marcinbauer-ohf/voice-pe-casita-face/images/IMG_7611.jpeg

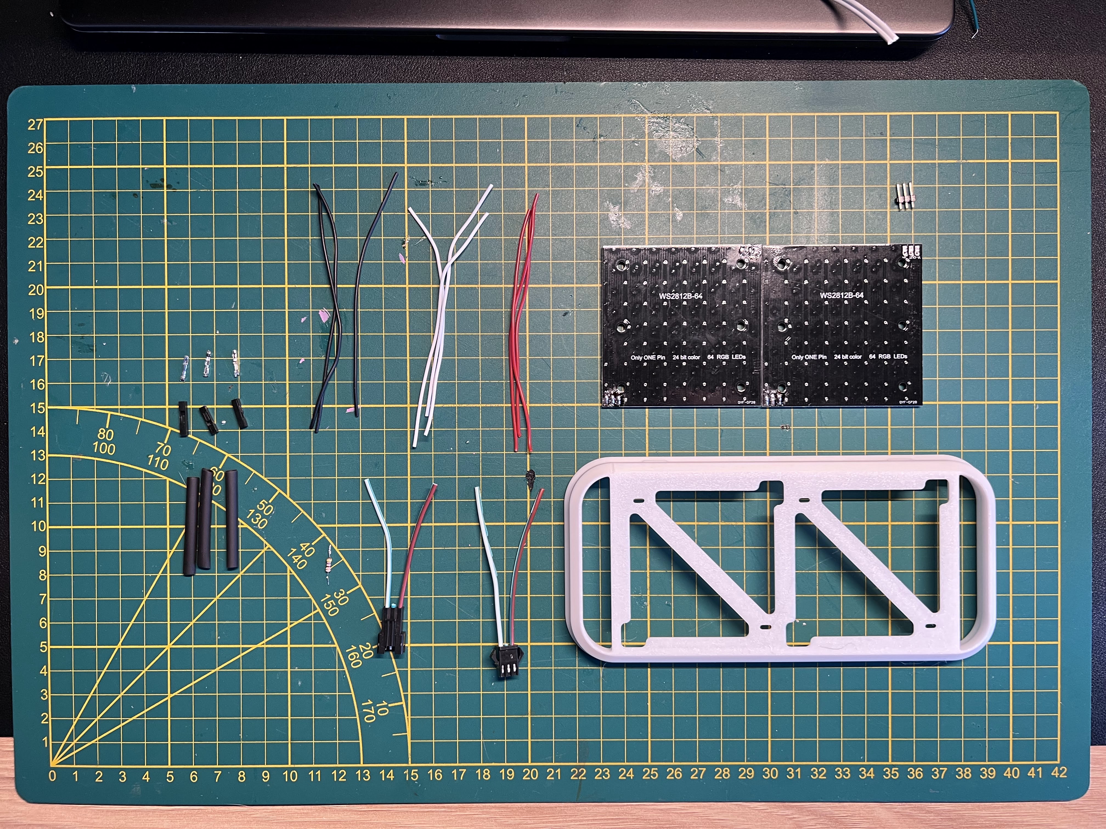
images/IMG_7611.jpeg
