marcinbauer-ohf/voice-pe-casita-face/images/IMG_7614.jpeg

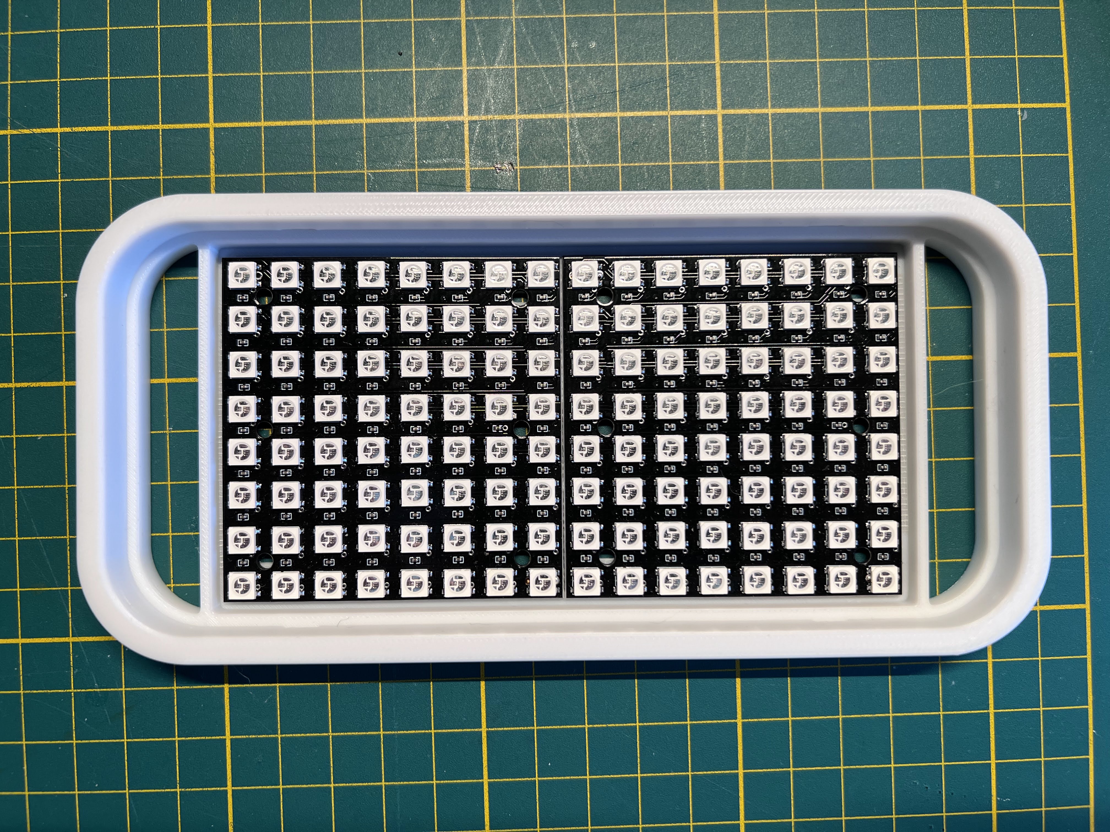
images/IMG_7614.jpeg
