marcinbauer-ohf/voice-pe-casita-face/images/IMG_7622.jpeg

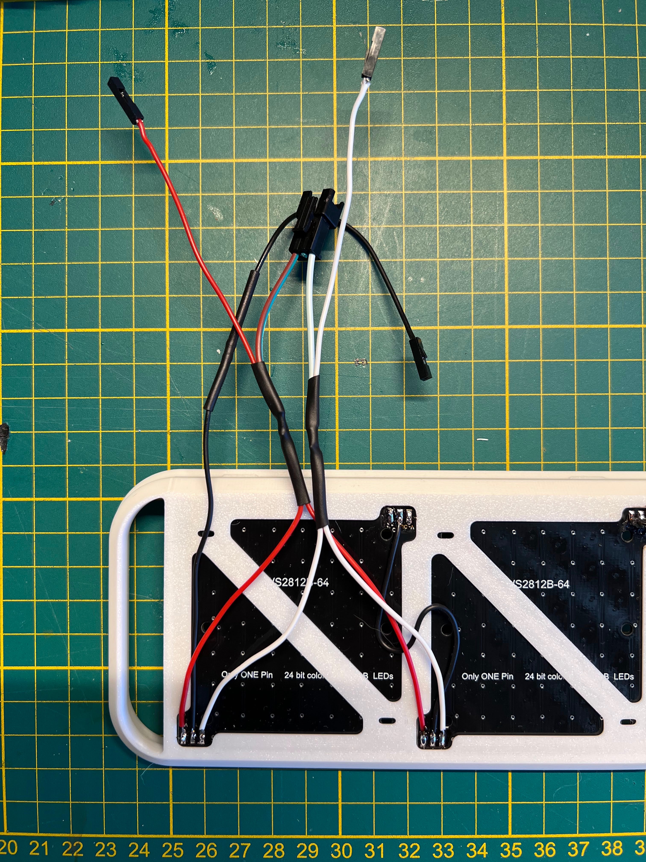
images/IMG_7622.jpeg
