marcinbauer-ohf/voice-pe-casita-face/images/IMG_7649.jpeg

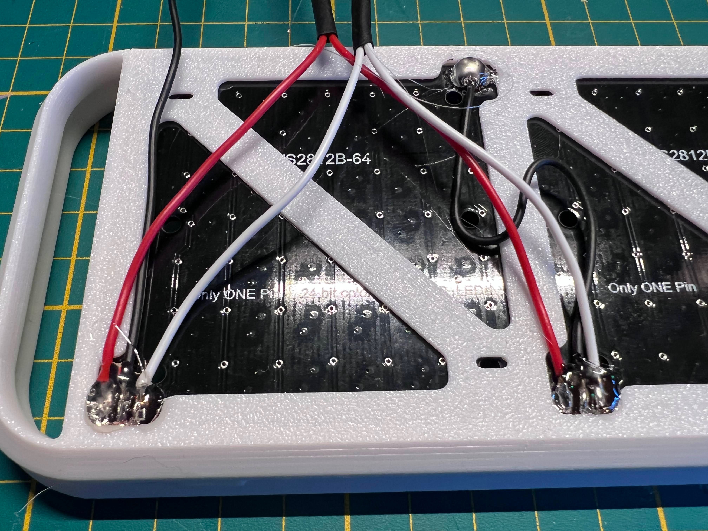
images/IMG_7649.jpeg
