marcinbauer-ohf/voice-pe-casita-face/images/IMG_7650.jpeg

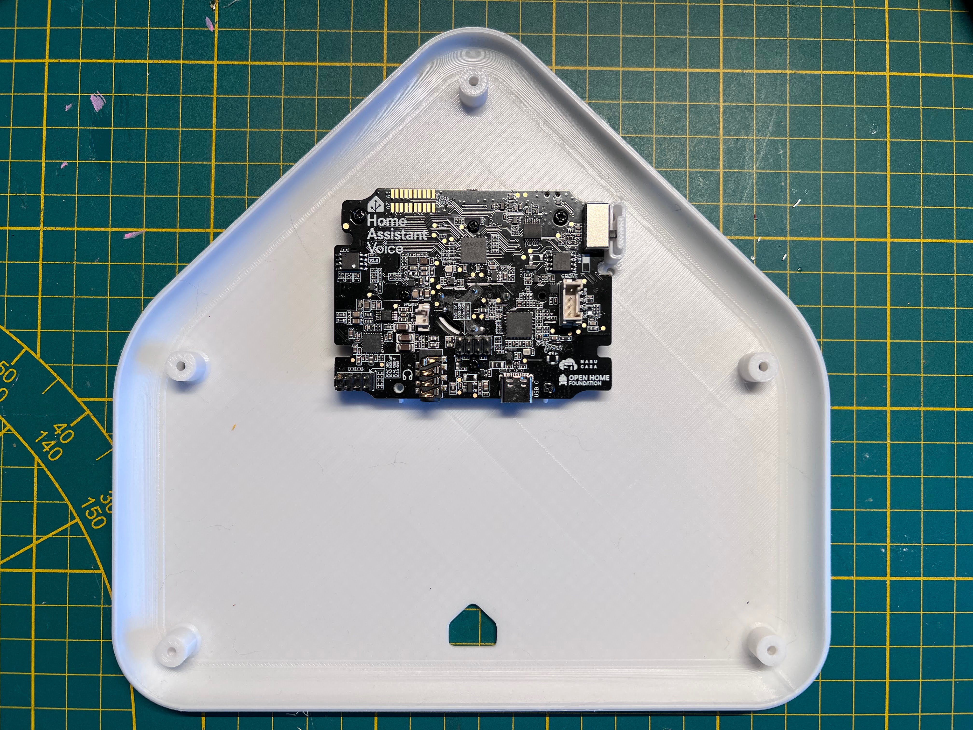
images/IMG_7650.jpeg
