marcinbauer-ohf/voice-pe-casita-face/images/IMG_7652.jpeg

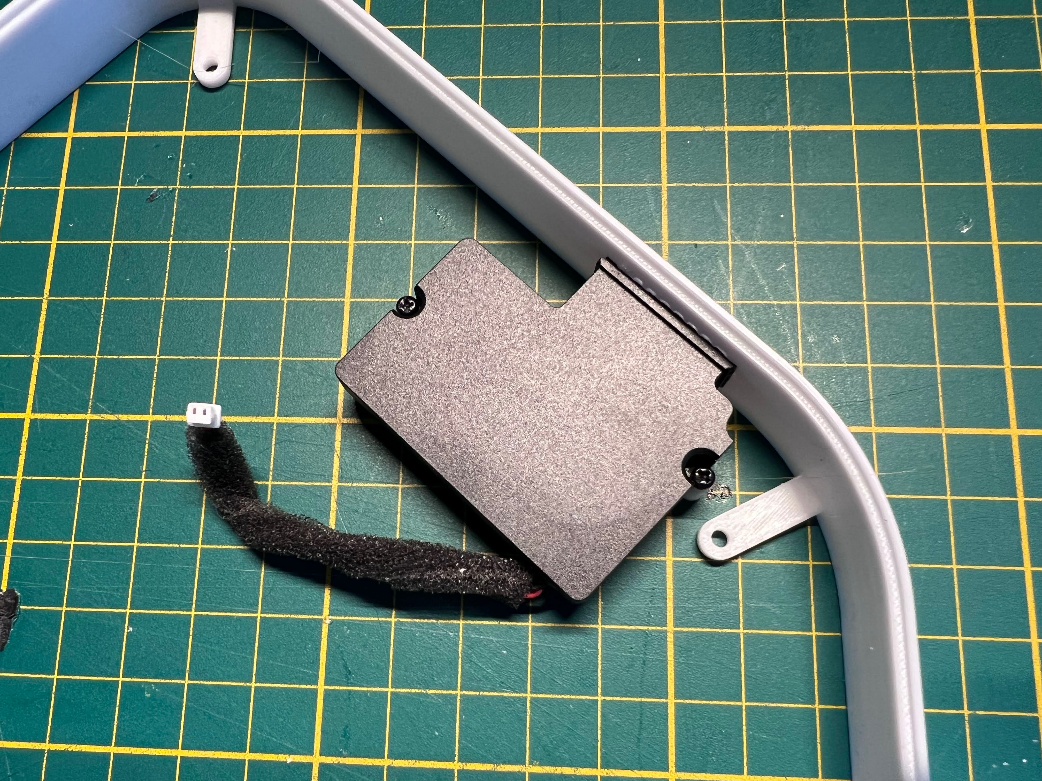
images/IMG_7652.jpeg
