marcinbauer-ohf/voice-pe-casita-face/images/IMG_7655.jpeg

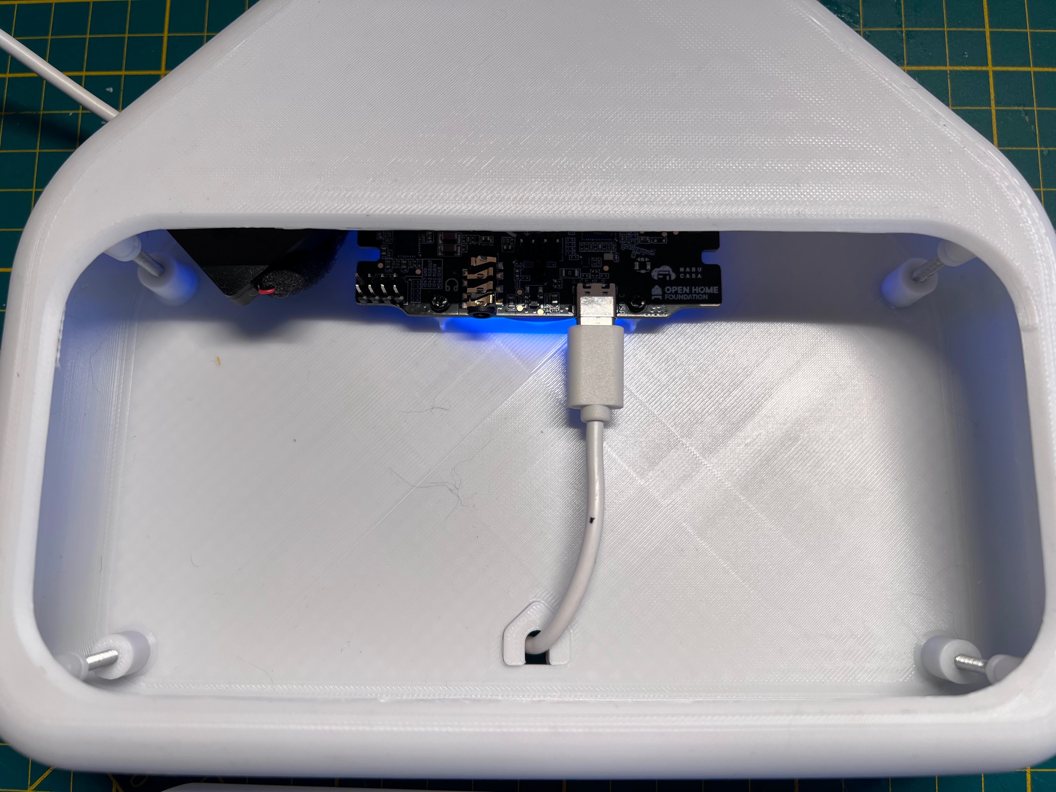
images/IMG_7655.jpeg
