marcinbauer-ohf/voice-pe-casita-face/images/IMG_7656.jpeg

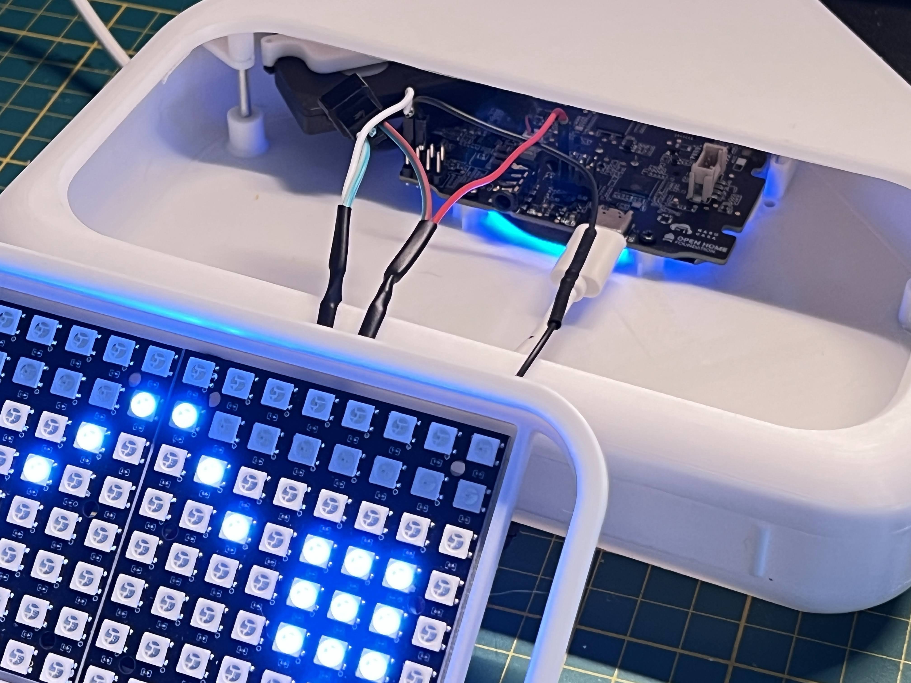
images/IMG_7656.jpeg
