marcinbauer-ohf/voice-pe-casita-face/images/IMG_7657.jpeg

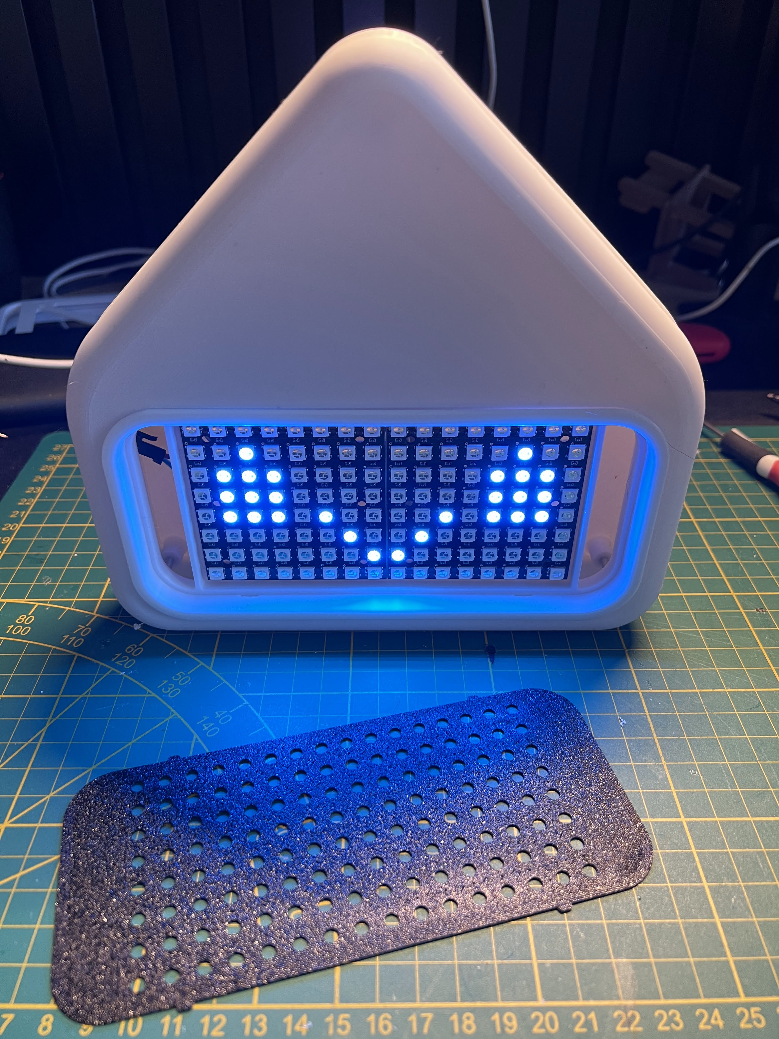
images/IMG_7657.jpeg
