marcinbauer-ohf/voice-pe-casita-face/images/IMG_7658.jpeg

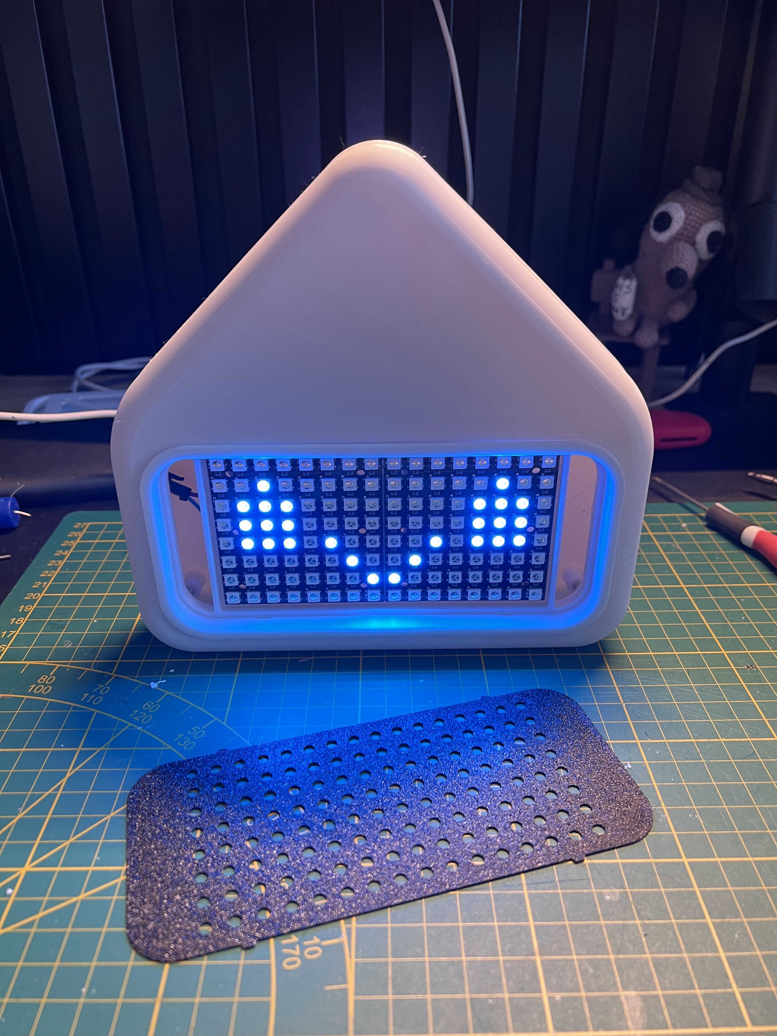
images/IMG_7658.jpeg
