marcinbauer-ohf/voice-pe-casita-face/images/IMG_7659.jpeg

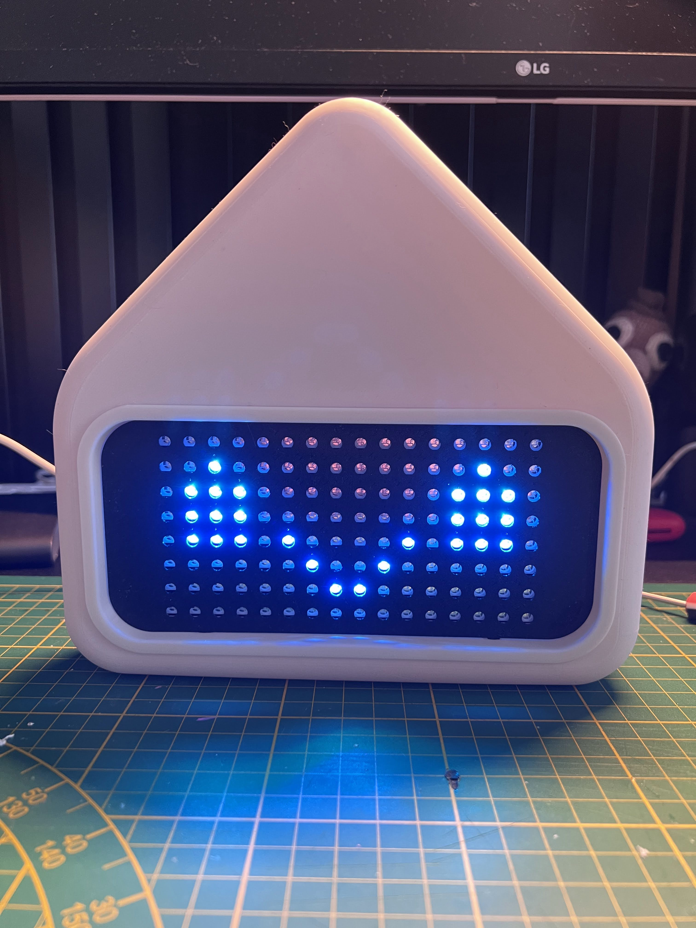
images/IMG_7659.jpeg
