marcinbauer-ohf/voice-pe-casita-face/images/IMG_7660.jpeg

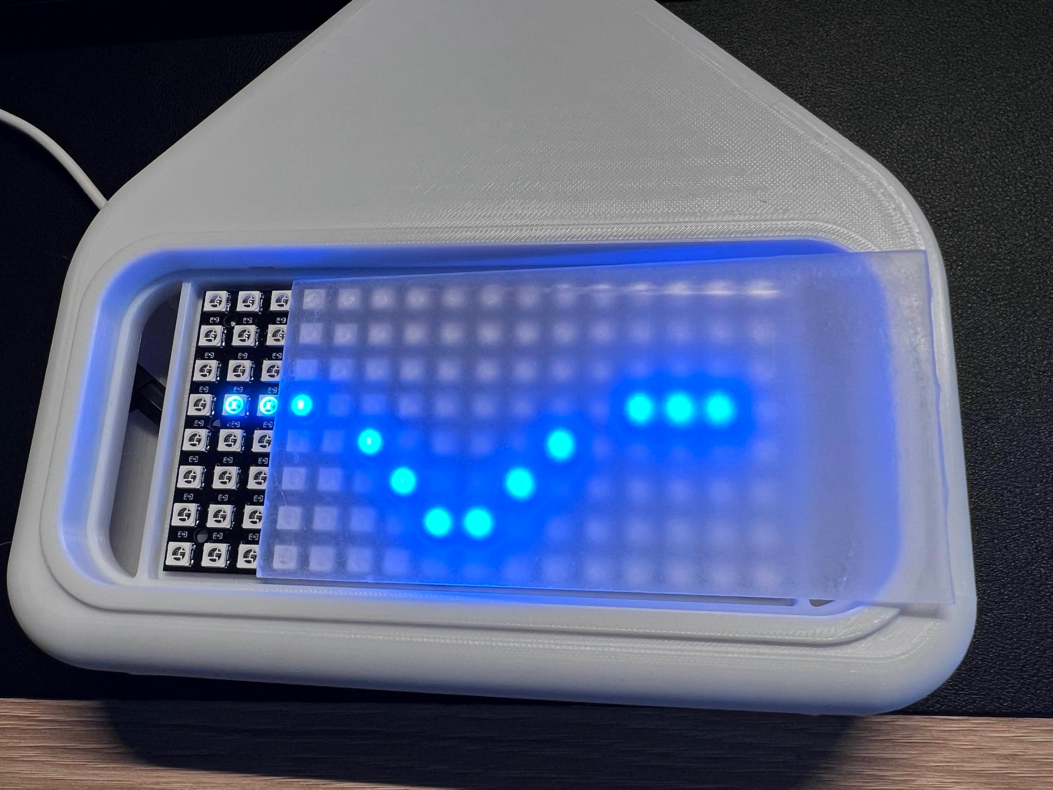
images/IMG_7660.jpeg
