marcinbauer-ohf/voice-pe-casita-face/images/IMG_7661.jpeg

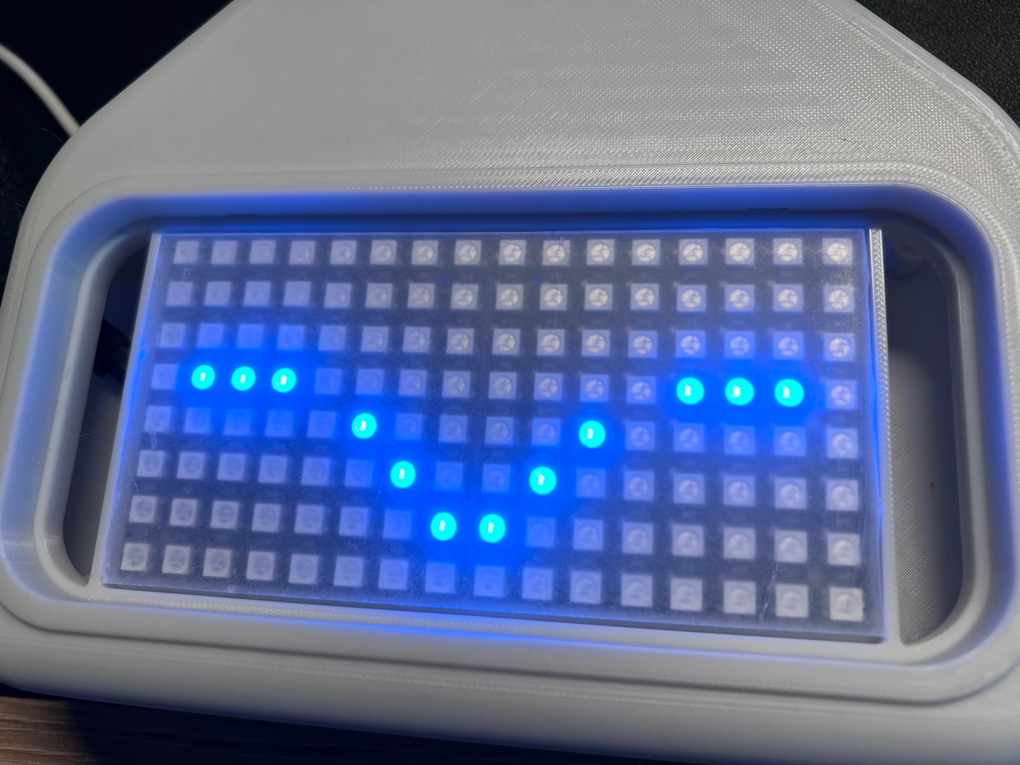
images/IMG_7661.jpeg
