marcinbauer-ohf/voice-pe-casita-face/images/IMG_7662.jpeg

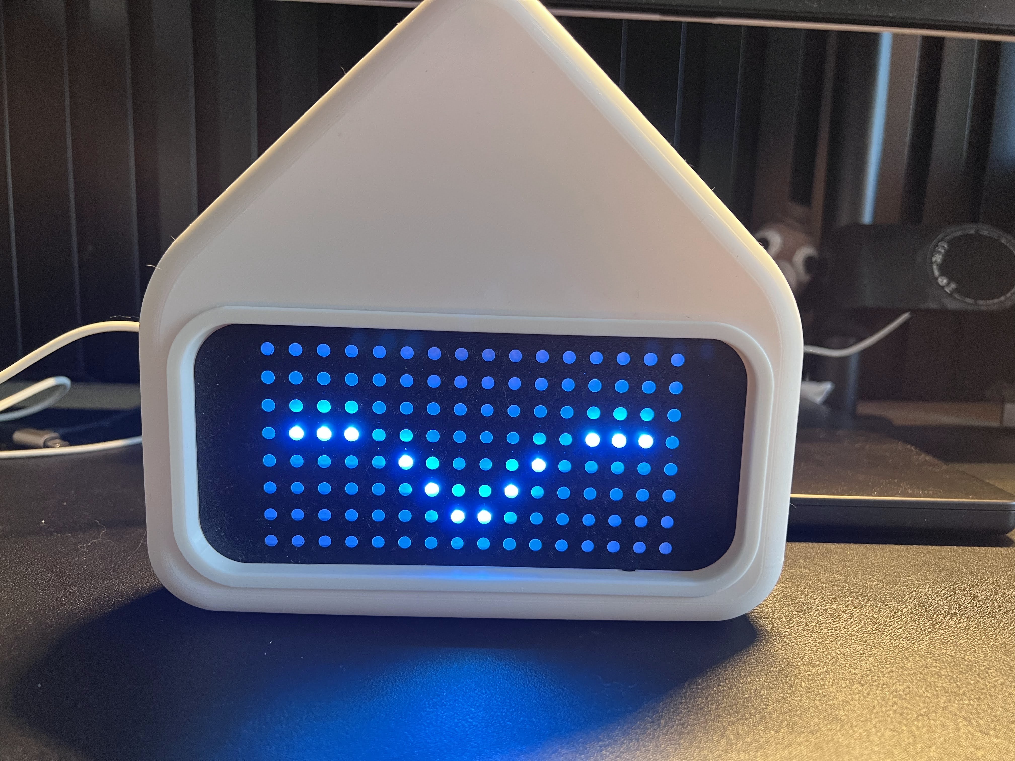
images/IMG_7662.jpeg
