marcinbauer-ohf/voice-pe-casita-face/images/IMG_7706.jpeg

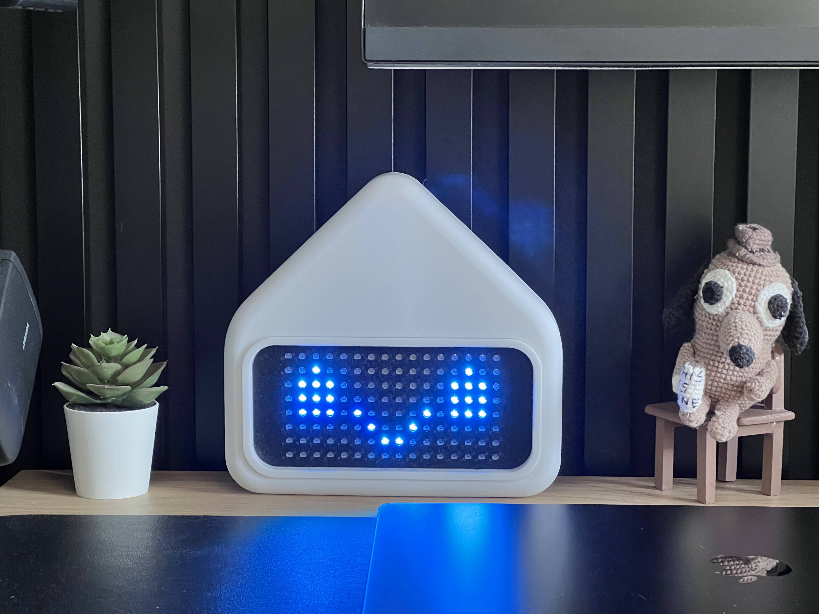
images/IMG_7706.jpeg
