marcinbauer-ohf/voice-pe-casita-face/images/IMG_7618.jpeg

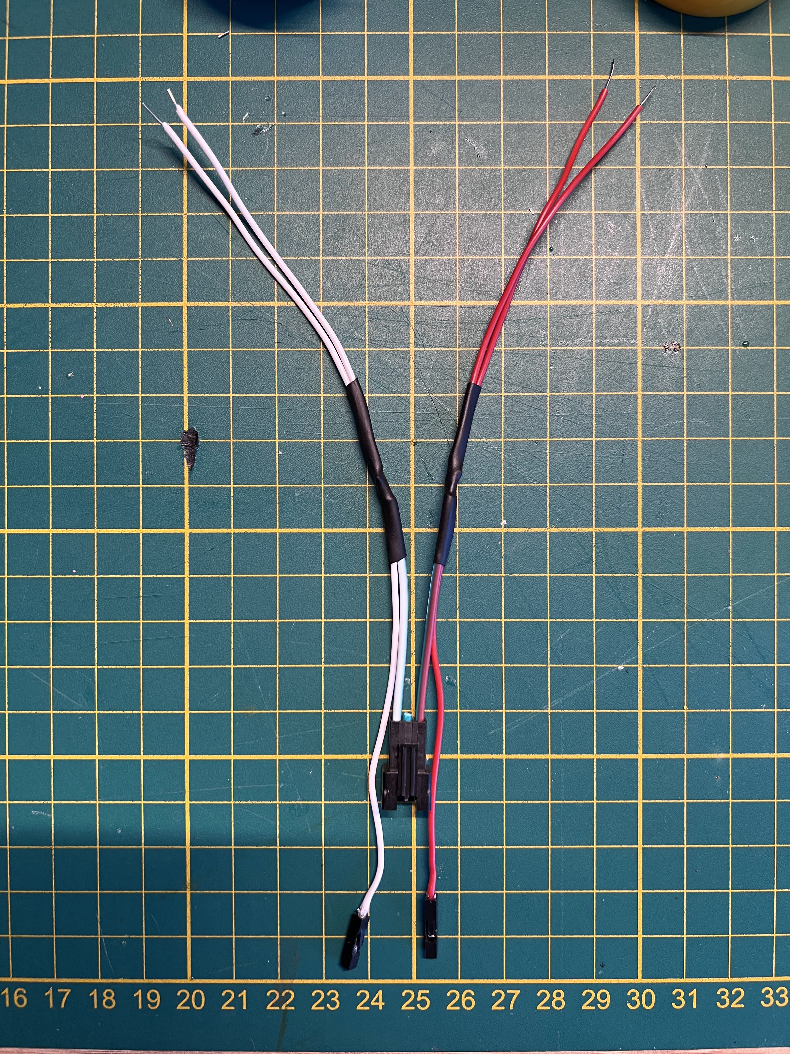
images/IMG_7618.jpeg
